akira215/mHeat/PCB/production/8071787a_y5/yg/GBR_11728107_1_snapshot.png

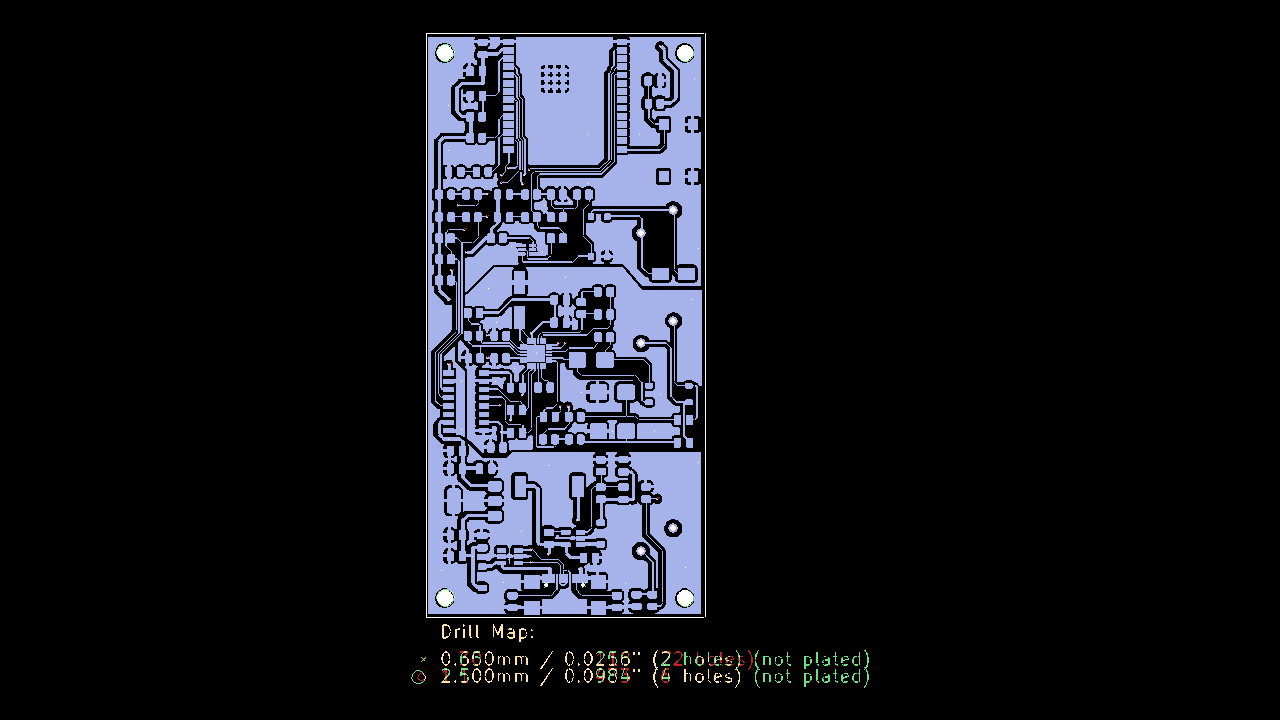
PCB/production/8071787a_y5/yg/GBR_11728107_1_snapshot.png
