akira215/mHeat/PCB/production/8071787a_y5/yg/GBR_11728107_1_top.png

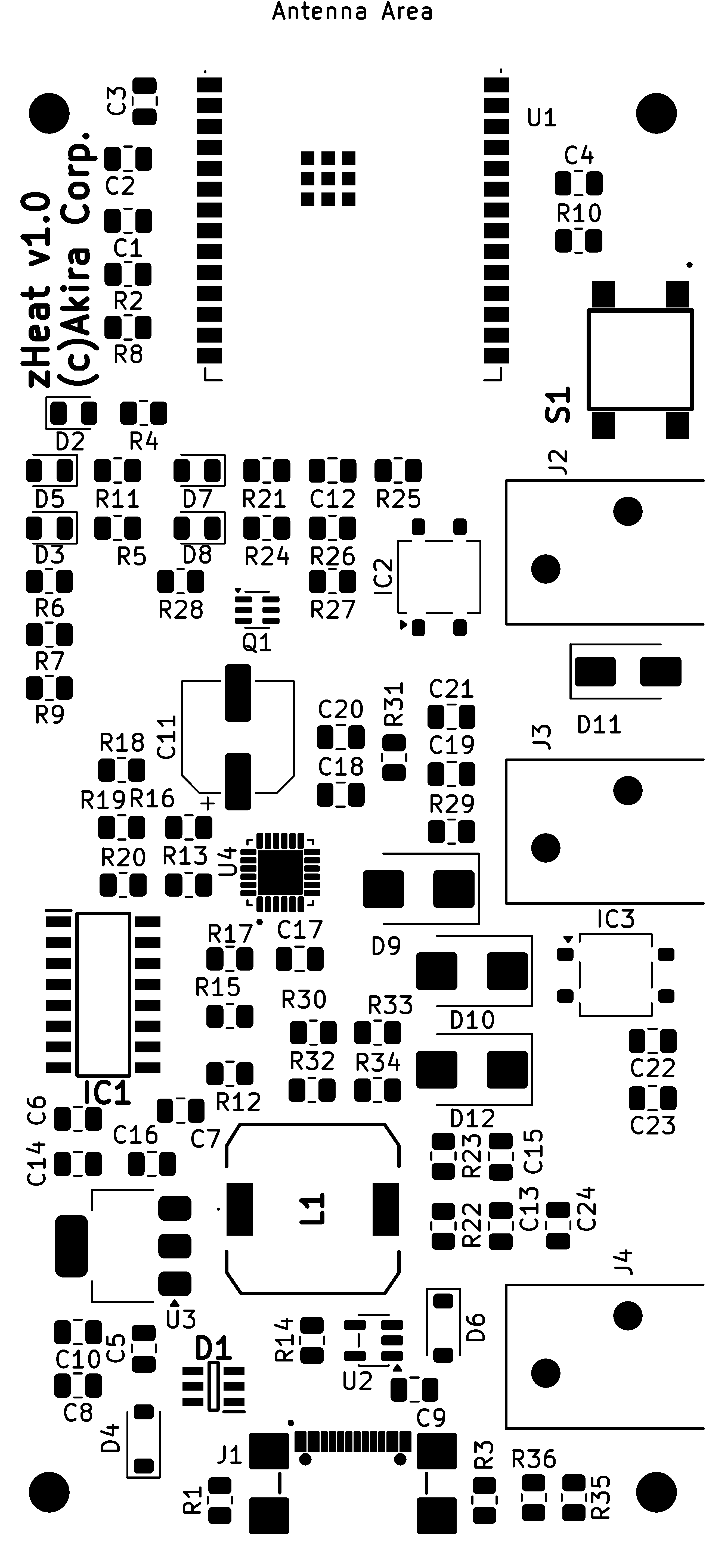
PCB/production/8071787a_y5/yg/GBR_11728107_1_top.png
